IQTLabs/Teachable-Camera-Hardware/design-files/design-1/solidworks/case-lid.SLDPRT

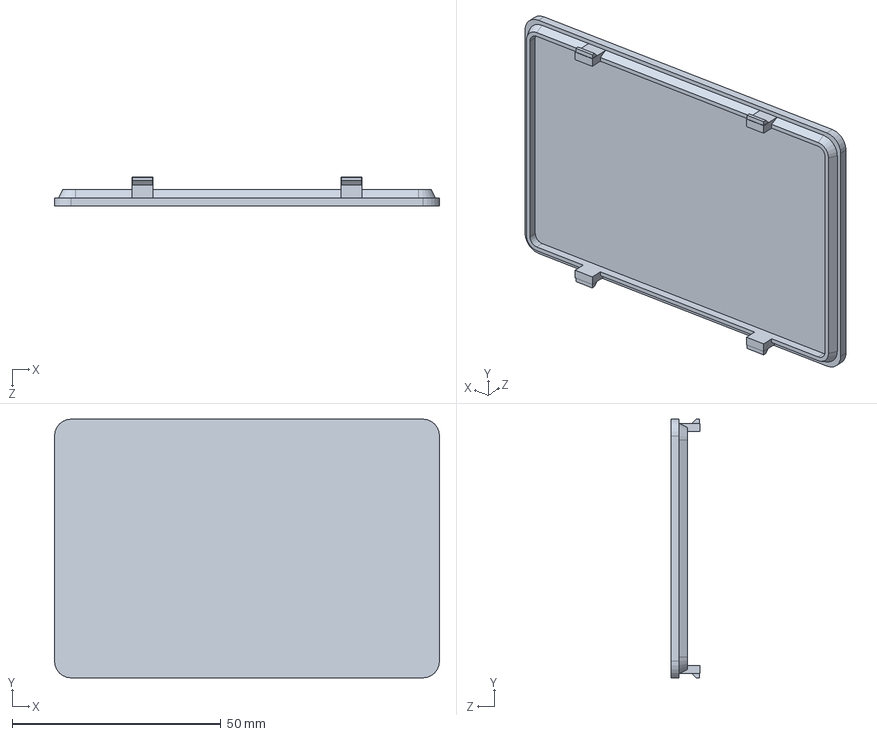
[picture p25: CAD file, 2020-08-20]
design-files/design-1/solidworks/case-lid.SLDPRT
92.1 x 61.9 x 7.00 mm
