IQTLabs/Teachable-Camera-Hardware/design-files/design-3/solidworks/goal-zero-boulder-50.SLDPRT

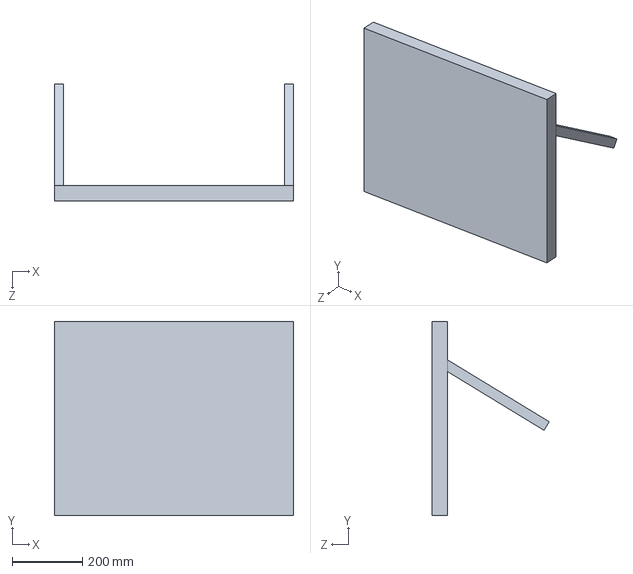
[picture p26: CAD file, 2020-08-04]
design-files/design-3/solidworks/goal-zero-boulder-50.SLDPRT
679.4 x 552.5 x 334.0 mm
