IQTLabs/Teachable-Camera-Hardware/design-files/design-3/solidworks/yeti-200x.SLDPRT

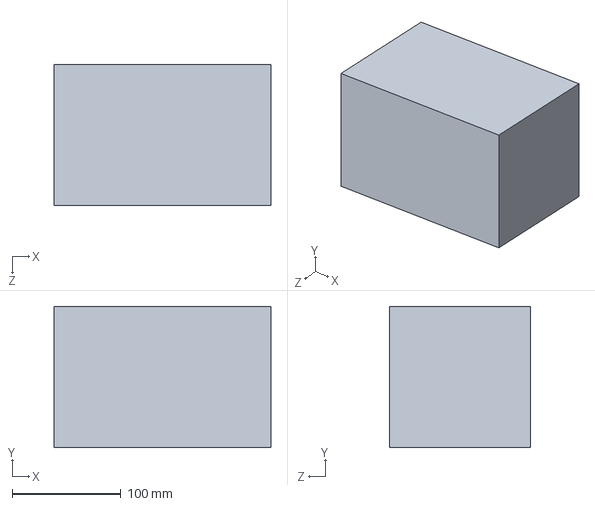
[picture p27: CAD file, 2020-08-04]
design-files/design-3/solidworks/yeti-200x.SLDPRT
200.0 x 130.0 x 130.0 mm
