IQTLabs/Teachable-Camera-Hardware/design-files/design-3/solidworks/unifi-g3-pro-camera.SLDPRT

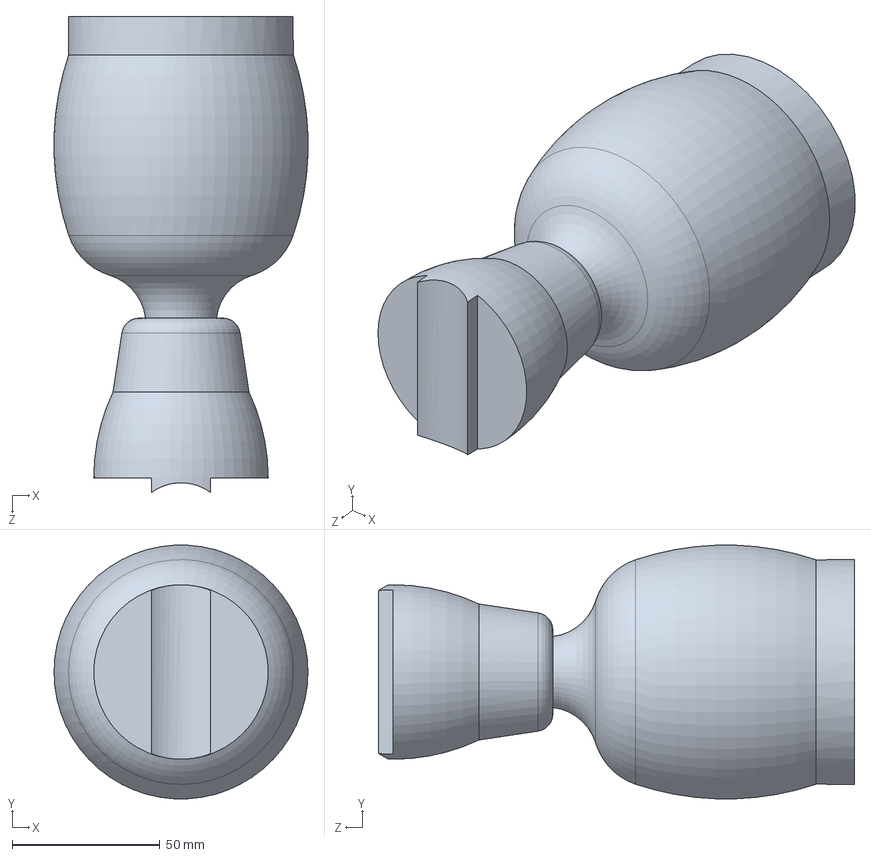
[picture p28: CAD file, 2020-08-04]
design-files/design-3/solidworks/unifi-g3-pro-camera.SLDPRT
85.9 x 85.7 x 161.0 mm
