IQTLabs/Teachable-Camera-Hardware/design-files/design-3/solidworks/unifi-g3-pro-camera-tripod-mount.SLDPRT

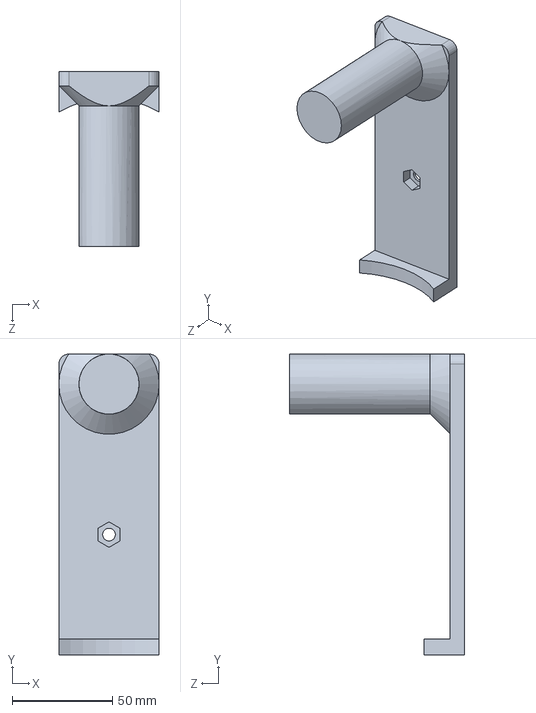
[picture p29: CAD file, 2020-08-04]
design-files/design-3/solidworks/unifi-g3-pro-camera-tripod-mount.SLDPRT
50.0 x 150.0 x 87.0 mm
